mnemocron/FeatherCandle/Software/FeatherCandleFeather/data7x15flip.h

const uint8_t PROGMEM anim[] = {
  0X00, 0X6E,   //  frame000.png 0 6 0 14
  0X00, 0X00, 0X00, 0X00, 0X00, 0X00, 0X00,
  0X00, 0X00, 0X00, 0X00, 0X00, 0X00, 0X00,
  0X00, 0X03, 0X00, 0X00, 0X01, 0X00, 0X00,
  0X00, 0X15, 0X01, 0X00, 0X0C, 0X01, 0X00,
  0X00, 0X3E, 0X0F, 0X03, 0X34, 0X01, 0X00,
  0X00, 0X6B, 0X47, 0X20, 0X81, 0X02, 0X00,
  0X00, 0X75, 0XA3, 0X6B, 0XBF, 0X03, 0X00,
  0X00, 0X5C, 0XDD, 0XAB, 0XC1, 0X02, 0X00,
  0X00, 0X44, 0XFA, 0XC1, 0XB2, 0X01, 0X00,
  0X00, 0X1E, 0XF7, 0XD1, 0X99, 0X00, 0X00,
  0X00, 0X07, 0XCF, 0XDD, 0X57, 0X00, 0X00,
  0X00, 0X01, 0X8C, 0XE5, 0X1C, 0X00, 0X00,
  0X00, 0X00, 0X39, 0XBC, 0X05, 0X00, 0X00,
  0X00, 0X00, 0X0A, 0X42, 0X00, 0X00, 0X00,
  0X00, 0X00, 0X00, 0X01, 0X00, 0X00, 0X00,
  0X13, 0X5D,   //  frame001.png 1 5 3 13
  0X16, 0X01, 0X00, 0X0D, 0X01,
  0X3F, 0X10, 0X03, 0X34, 0X01,
  0X6D, 0X4B, 0X23, 0X7F, 0X02,
  0X73, 0XA3, 0X70, 0XB8, 0X02,
  0X5C, 0XDB, 0XAD, 0XB8, 0X02,
  0X44, 0XFA, 0XC6, 0XA9, 0X01,
  0X1D, 0XF7, 0XD6, 0X8D, 0X00,
  0X07, 0XD1, 0XE5, 0X48, 0X00,
  0X01, 0X8D, 0XE7, 0X16, 0X00,
  0X00, 0X3D, 0XB8, 0X03, 0X00,
  0X00, 0X0C, 0X3B, 0X00, 0X00,
  0X13, 0X5E,   //  frame002.png 1 5 3 14
  0X18, 0X01, 0X00, 0X0E, 0X00,
  0X42, 0X12, 0X04, 0X35, 0X01,
  0X72, 0X50, 0X27, 0X7D, 0X01,
  0X77, 0XA7, 0X77, 0XB2, 0X01,
  0X5B, 0XE0, 0XB4, 0XAB, 0X01,
  0X42, 0XFC, 0XCD, 0X9F, 0X00,
  0X1C, 0XF7, 0XDD, 0X7C, 0X00,
  0X07, 0XD4, 0XEF, 0X39, 0X00,
  0X01, 0X91, 0XE5, 0X0F, 0X00,
  0X00, 0X42, 0XA7, 0X01, 0X00,
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
  0X78, 0X9D, 0X70, 0XAF, 0X01,
  0X62, 0XD8, 0XB4, 0XAF, 0X01,
  0X4B, 0XF7, 0XCD, 0XA3, 0X01,
  0X25, 0XFA, 0XDB, 0X88, 0X00,
  0X0A, 0XD8, 0XE7, 0X47, 0X00,
  0X01, 0X9D, 0XE7, 0X17, 0X00,
  0X00, 0X4C, 0XBF, 0X03, 0X00,
  0X00, 0X13, 0X4F, 0X00, 0X00,
  0XFF, 0XFF, 0XFF, };

// 17505 bytes
